dkrygsman/autotiller/autotillerki.kicad_sch

## KiCad design autotillerki.kicad_sch (2024-12-11)

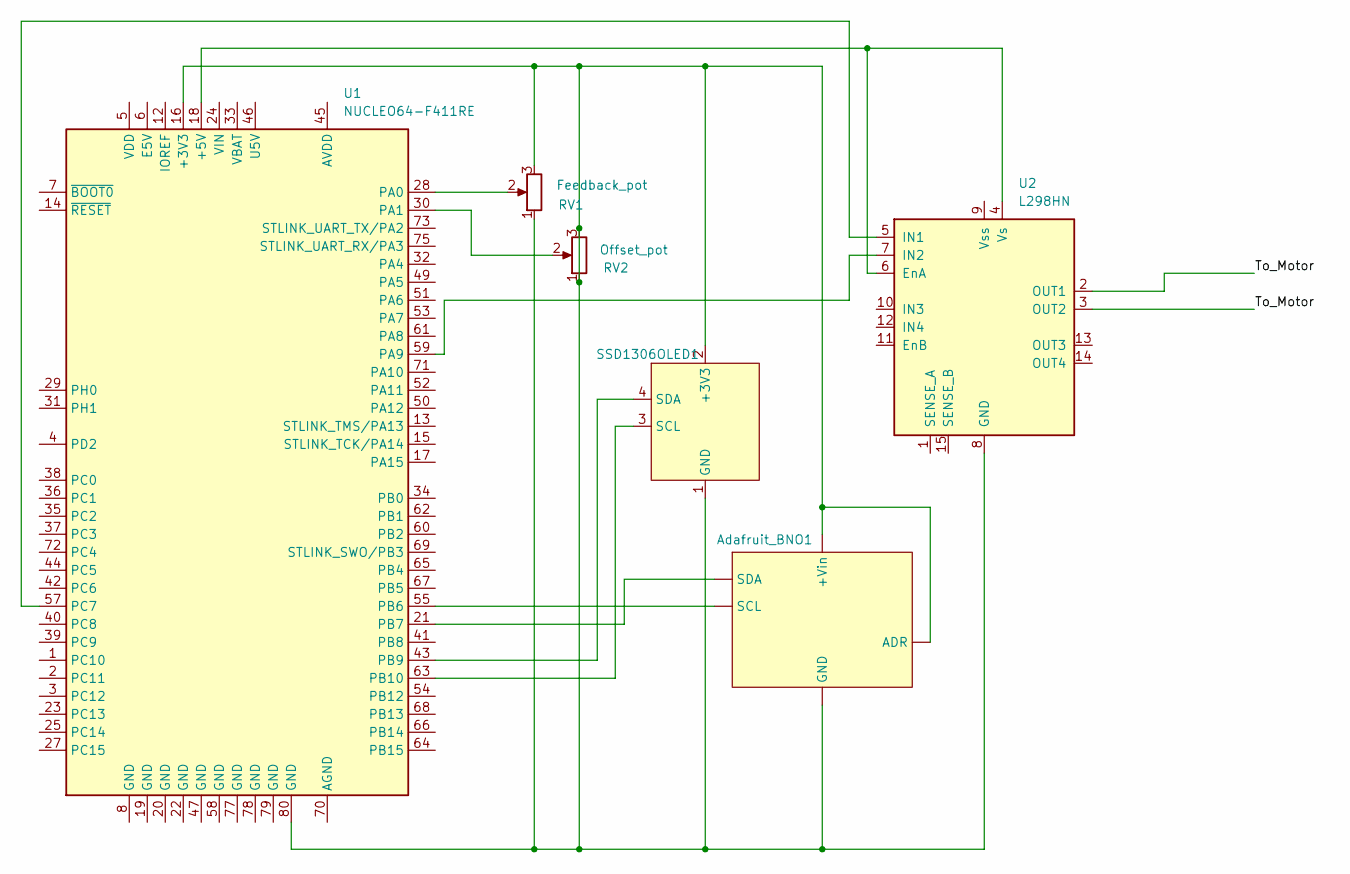
[picture p15: schematic autotillerki.kicad_sch]

Parts:
Adafruit_BNO1: (no value)
RV1: Feedback_pot
RV2: Offset_pot
SSD1306OLED1: (no value)
U1: NUCLEO64-F411RE; ST_Morpho_Connector_144_STLink
U2: L298HN; TO-220-15_P2.54x2.54mm_StaggerOdd_Lead5.84mm_TabDown

Connections:
unnamed: Adafruit_BNO1., RV1.1, RV1.3, RV2.1, RV2.3, SSD1306OLED1.1 (GND), SSD1306OLED1.2 (+3V3), U1.16 (+3V3), U1.21 (PB7), U1.55 (PB6), U1.80 (GND), U2.8 (GND)
unnamed: RV1.2, U1.28 (PA0)
unnamed: RV2.2, U1.30 (PA1)
unnamed: SSD1306OLED1.3 (SCL), U1.63 (PB10)
unnamed: SSD1306OLED1.4 (SDA), U1.43 (PB9)
unnamed: U1.18 (+5V), U2.4 (Vs), U2.6 (EnA)
unnamed: U1.57 (PC7), U2.5 (IN1)
unnamed: U1.59 (PA9), U2.7 (IN2)
To_Motor: U2.2 (OUT1), U2.3 (OUT2)
